jf-lab/chendoscope/camera-interface-board-PCB/camera-interface-board.sch

## KiCad design camera-interface-board-PCB/camera-interface-board.sch (2018-02-02)

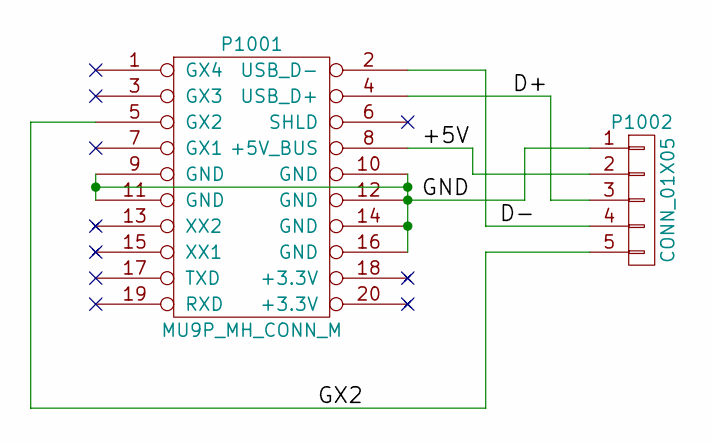
[picture p7: schematic camera-interface-board.sch]

Parts:
P1001: MU9P_MH_CONN_M; DF12A-20DS-M
P1002: CONN_01X05; SMD_05_Hole

Connections:
+5V: P1001.8 (+5V_BUS), P1002.2
D+: P1001.4 (USB_D+), P1002.3
D-: P1001.2 (USB_D-), P1002.4
GND: P1001.9 (GND), P1001.10 (GND), P1001.11 (GND), P1001.12 (GND), P1001.14 (GND), P1001.16 (GND), P1002.1
GX2: P1001.5 (GX2), P1002.5
